sh7vashrestha/DeltaArm/Diagrams/Block Diagram.png

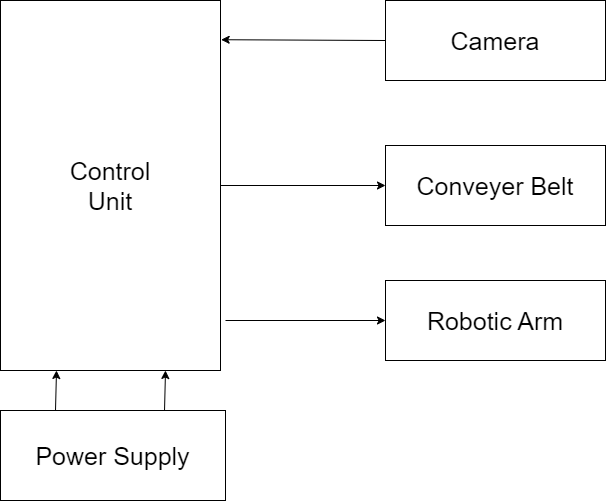
Diagrams/Block Diagram.png
