sh7vashrestha/DeltaArm/Arm-3D-Modelled-Parts/aluminium holder.png

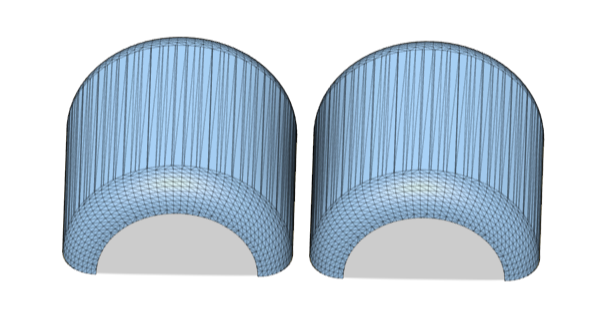
Arm-3D-Modelled-Parts/aluminium holder.png
