sh7vashrestha/DeltaArm/Arm-3D-Modelled-Parts/base.png

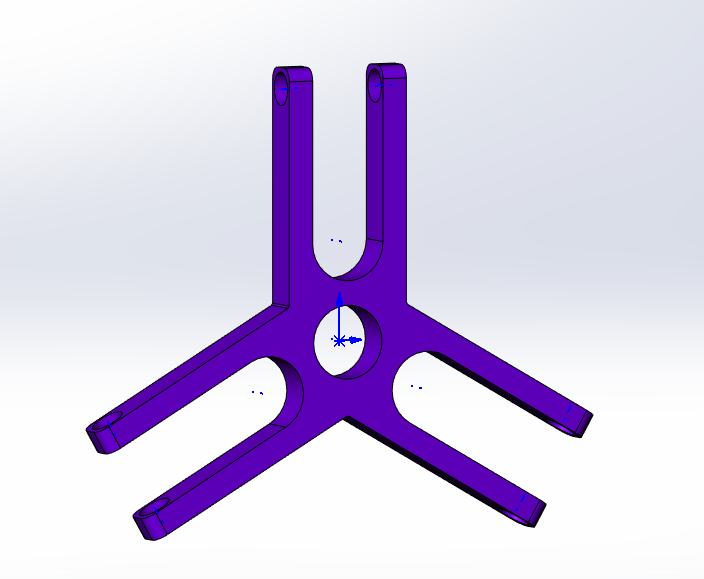
Arm-3D-Modelled-Parts/base.png
