sh7vashrestha/DeltaArm/Arm-3D-Modelled-Parts/cap.png

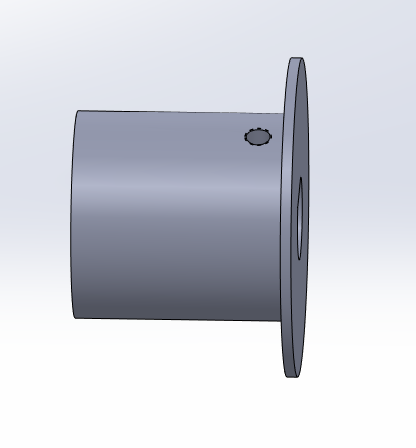
Arm-3D-Modelled-Parts/cap.png
