sh7vashrestha/DeltaArm/Arm-3D-Modelled-Parts/stepper motor holder.png

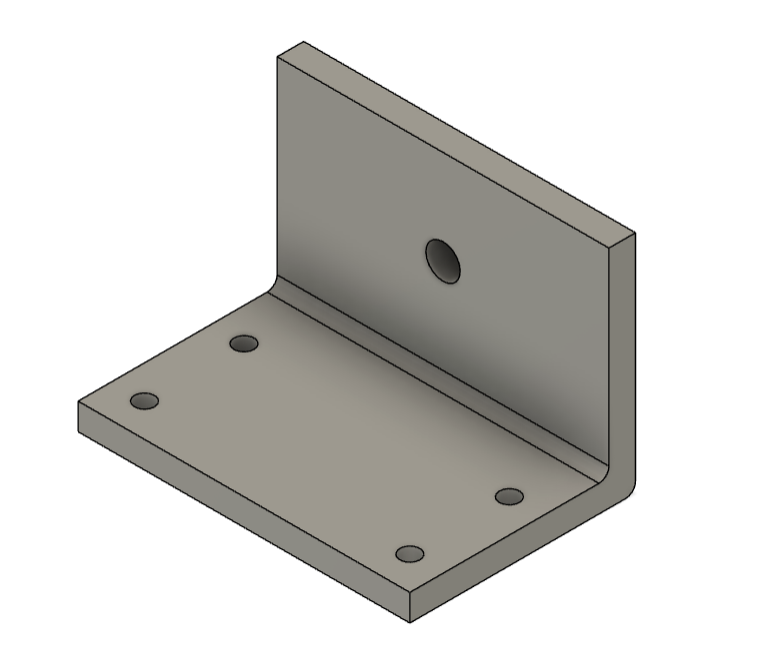
Arm-3D-Modelled-Parts/stepper motor holder.png
